ananthyoj26-a11y/GreenVolt-SIH-2026/media/prototype_photos/WhatsApp Image 2026-04-01 at 5.28.12 PM.jpeg

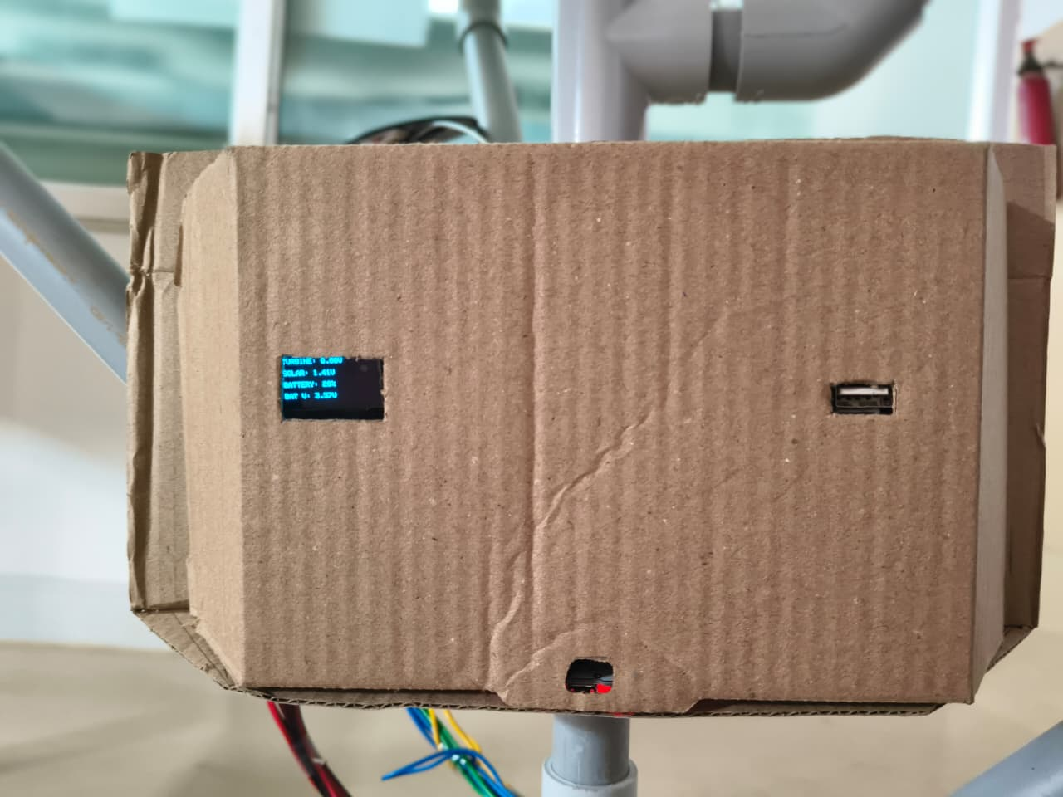
media/prototype_photos/WhatsApp Image 2026-04-01 at 5.28.12 PM.jpeg
