ananthyoj26-a11y/GreenVolt-SIH-2026/simulation/resources/previewImage.jpeg

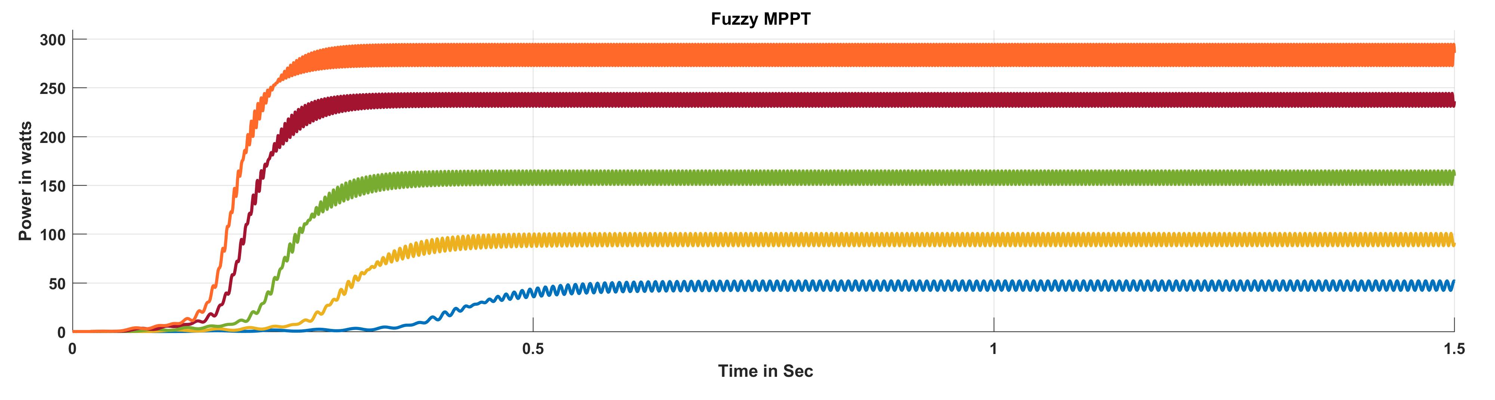
simulation/resources/previewImage.jpeg
