ananthyoj26-a11y/GreenVolt-SIH-2026/software/dashboard/dashboard1.jpeg

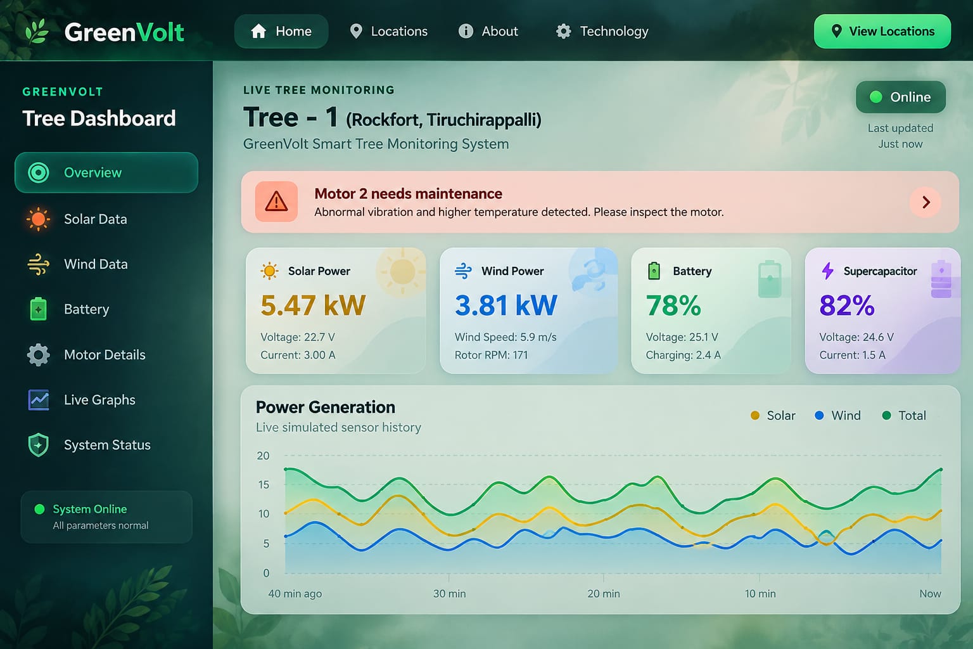
software/dashboard/dashboard1.jpeg
