ananthyoj26-a11y/GreenVolt-SIH-2026/software/dashboard/dashboard2.jpeg

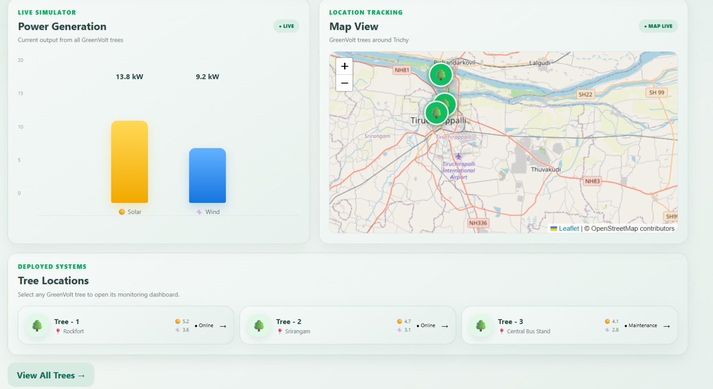
software/dashboard/dashboard2.jpeg
