ananthyoj26-a11y/GreenVolt-SIH-2026/software/dashboard/dashboard3.jpeg

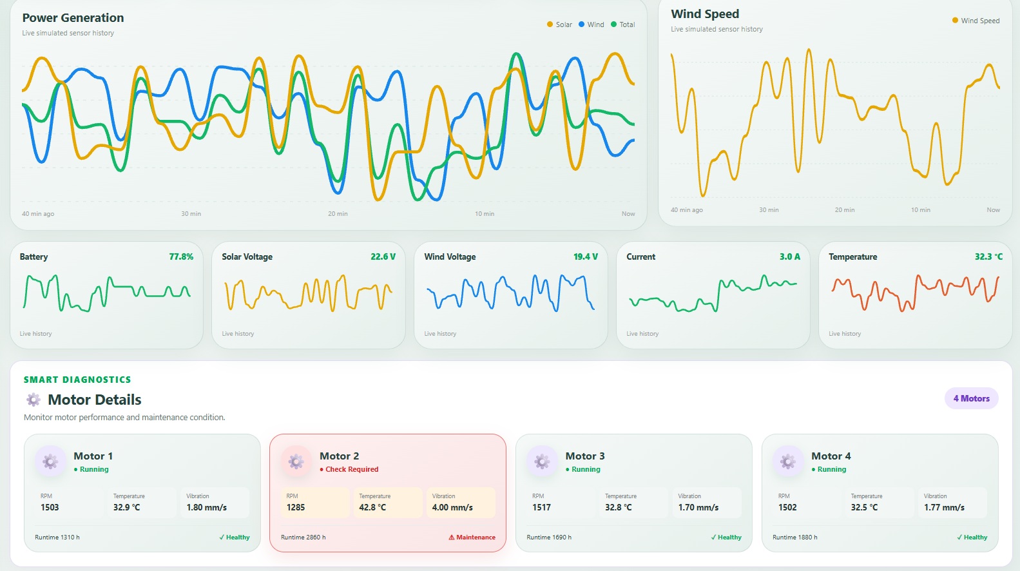
software/dashboard/dashboard3.jpeg
